leizhenyu97/WISP/Ver061/Firmware/ad7124_ble_tx_timer_LP/AD7124.h

// Low-level AD7124 register and SPI declarations for the firmware data path.
// This header defines the software shadow-register table and the helpers that read and write the device.

#ifndef _AD7124_H
#define _AD7124_H

#include "Arduino.h"

#ifdef  __cplusplus
extern "C" {
#endif

// Indexes into the software shadow-register table, not raw wire addresses.
enum ad7124_registers {
        AD7124_Status = 0x00,
        AD7124_ADC_Control,
        AD7124_Data,
        AD7124_IOCon1,
        AD7124_IOCon2,
        AD7124_ID,
        AD7124_Error,
        AD7124_Error_En,
        AD7124_Mclk_Count,
        AD7124_Channel_0,
        AD7124_Channel_1,
        AD7124_Channel_2,
        AD7124_Channel_3,
        AD7124_Channel_4,
        AD7124_Channel_5,
        AD7124_Channel_6,
        AD7124_Channel_7,
        AD7124_Channel_8,
        AD7124_Channel_9,
        AD7124_Channel_10,
        AD7124_Channel_11,
        AD7124_Channel_12,
        AD7124_Channel_13,
        AD7124_Channel_14,
        AD7124_Channel_15,
        AD7124_Config_0,
        AD7124_Config_1,
        AD7124_Config_2,
        AD7124_Config_3,
        AD7124_Config_4,
        AD7124_Config_5,
        AD7124_Config_6,
        AD7124_Config_7,
        AD7124_Filter_0,
        AD7124_Filter_1,
        AD7124_Filter_2,
        AD7124_Filter_3,
        AD7124_Filter_4,
        AD7124_Filter_5,
        AD7124_Filter_6,
        AD7124_Filter_7,
        AD7124_Offset_0,
        AD7124_Offset_1,
        AD7124_Offset_2,
        AD7124_Offset_3,
        AD7124_Offset_4,
        AD7124_Offset_5,
        AD7124_Offset_6,
        AD7124_Offset_7,
        AD7124_Gain_0,
        AD7124_Gain_1,
        AD7124_Gain_2,
        AD7124_Gain_3,
        AD7124_Gain_4,
        AD7124_Gain_5,
        AD7124_Gain_6,
        AD7124_Gain_7,
        AD7124_REG_NO
    };

     typedef enum _ad7124_reg_access{
        AD7124_RW = 1,   /* Read and Write */
        AD7124_R  = 2,   /* Read only */
        AD7124_W  = 3,   /* Write only */
    } ad7124_reg_access; // Software access permissions for entries in regs[].

    /*! Device register info */
    typedef struct _ad7124_st_reg {
        int32_t addr;   // Raw AD7124 register address used in the communication byte.
        int32_t value;  // Shadowed register value stored in software.
        uint8_t _size;  // Register payload width in bytes.
        uint8_t rw;     // Access permission from ad7124_reg_access.
    } ad7124_st_reg;

    /* AD7124 raw register addresses placed in the first SPI command byte. */
    enum AD7124_reg_map  {
        COMM_REG     = 0x00,
        STATUS_REG   = 0x00,
        ADC_CTRL_REG = 0x01,
        DATA_REG     = 0x02,
        IO_CTRL1_REG = 0x03,
        IO_CTRL2_REG = 0x04,
        ID_REG       = 0x05,
        ERR_REG      = 0x06,
        ERREN_REG    = 0x07,
        CH0_MAP_REG  = 0x09,
        CH1_MAP_REG  = 0x0A,
        CH2_MAP_REG  = 0x0B,
        CH3_MAP_REG  = 0x0C,
        CH4_MAP_REG  = 0x0D,
        CH5_MAP_REG  = 0x0E,
        CH6_MAP_REG  = 0x0F,
        CH7_MAP_REG  = 0x10,
        CH8_MAP_REG  = 0x11,
        CH9_MAP_REG  = 0x12,
        CH10_MAP_REG = 0x13,
        CH11_MAP_REG = 0x14,
        CH12_MAP_REG = 0x15,
        CH13_MAP_REG = 0x16,
        CH14_MAP_REG = 0x17,
        CH15_MAP_REG = 0x18,
        CFG0_REG     = 0x19,
        CFG1_REG     = 0x1A,
        CFG2_REG     = 0x1B,
        CFG3_REG     = 0x1C,
        CFG4_REG     = 0x1D,
        CFG5_REG     = 0x1E,
        CFG6_REG     = 0x1F,
        CFG7_REG     = 0x20,
        FILT0_REG    = 0x21,
        FILT1_REG    = 0x22,
        FILT2_REG    = 0x23,
        FILT3_REG    = 0x24,
        FILT4_REG    = 0x25,
        FILT5_REG    = 0x26,
        FILT6_REG    = 0x27,
        FILT7_REG    = 0x28,
        OFFS0_REG    = 0x29,
        OFFS1_REG    = 0x2A,
        OFFS2_REG    = 0x2B,
        OFFS3_REG    = 0x2C,
        OFFS4_REG    = 0x2D,
        OFFS5_REG    = 0x2E,
        OFFS6_REG    = 0x2F,
        OFFS7_REG    = 0x30,
        GAIN0_REG    = 0x31,
        GAIN1_REG    = 0x32,
        GAIN2_REG    = 0x33,
        GAIN3_REG    = 0x34,
        GAIN4_REG    = 0x35,
        GAIN5_REG    = 0x36,
        GAIN6_REG    = 0x37,
        GAIN7_REG    = 0x38,
    };

    /* Communication Register bits: these macros assemble the first SPI command byte. */
#define AD7124_COMM_REG_WEN    (0 << 7)
#define AD7124_COMM_REG_WR     (0 << 6)
#define AD7124_COMM_REG_RD     (1 << 6)
#define AD7124_COMM_REG_RA(x)  ((x) & 0x3F)

    /* Status Register bits */
#define AD7124_STATUS_REG_RDY          (1 << 7)
#define AD7124_STATUS_REG_ERROR_FLAG   (1 << 6)
#define AD7124_STATUS_REG_POR_FLAG     (1 << 4)
#define AD7124_STATUS_REG_CH_ACTIVE(x) ((x) & 0xF)

    /* ADC_Control Register bits */
#define AD7124_ADC_CTRL_REG_DOUT_RDY_DEL   (1 << 12)
#define AD7124_ADC_CTRL_REG_CONT_READ      (1 << 11)
#define AD7124_ADC_CTRL_REG_DATA_STATUS    (1 << 10)
#define AD7124_ADC_CTRL_REG_CS_EN          (1 << 9)
#define AD7124_ADC_CTRL_REG_REF_EN         (1 << 8)
#define AD7124_ADC_CTRL_REG_POWER_MODE(x)  (((x) & 0x3) << 6)
#define AD7124_ADC_CTRL_REG_MODE(x)        (((x) & 0xF) << 2)
#define AD7124_ADC_CTRL_REG_CLK_SEL(x)    (((x) & 0x3) << 0)

    /* IO_Control_1 Register bits */
#define AD7124_IO_CTRL1_REG_GPIO_DAT2     (1 << 23)
#define AD7124_IO_CTRL1_REG_GPIO_DAT1     (1 << 22)
#define AD7124_IO_CTRL1_REG_GPIO_CTRL2    (1 << 19)
#define AD7124_IO_CTRL1_REG_GPIO_CTRL1    (1 << 18)
#define AD7124_IO_CTRL1_REG_PDSW          (1 << 15)
#define AD7124_IO_CTRL1_REG_IOUT1(x)      (((x) & 0x7) << 11)
#define AD7124_IO_CTRL1_REG_IOUT0(x)      (((x) & 0x7) << 8)
#define AD7124_IO_CTRL1_REG_IOUT_CH1(x)   (((x) & 0xF) << 4)
#define AD7124_IO_CTRL1_REG_IOUT_CH0(x)   (((x) & 0xF) << 0)

    /*IO_Control_1 AD7124-8 specific bits */
#define AD7124_8_IO_CTRL1_REG_GPIO_DAT4     (1 << 23)
#define AD7124_8_IO_CTRL1_REG_GPIO_DAT3     (1 << 22)
#define AD7124_8_IO_CTRL1_REG_GPIO_DAT2     (1 << 21)
#define AD7124_8_IO_CTRL1_REG_GPIO_DAT1     (1 << 20)
#define AD7124_8_IO_CTRL1_REG_GPIO_CTRL4    (1 << 19)
#define AD7124_8_IO_CTRL1_REG_GPIO_CTRL3    (1 << 18)
#define AD7124_8_IO_CTRL1_REG_GPIO_CTRL2    (1 << 17)
#define AD7124_8_IO_CTRL1_REG_GPIO_CTRL1    (1 << 16)

    /* IO_Control_2 Register bits */
#define AD7124_IO_CTRL2_REG_GPIO_VBIAS7   (1 << 15)
#define AD7124_IO_CTRL2_REG_GPIO_VBIAS6   (1 << 14)
#define AD7124_IO_CTRL2_REG_GPIO_VBIAS5   (1 << 11)
#define AD7124_IO_CTRL2_REG_GPIO_VBIAS4   (1 << 10)
#define AD7124_IO_CTRL2_REG_GPIO_VBIAS3   (1 << 5)
#define AD7124_IO_CTRL2_REG_GPIO_VBIAS2   (1 << 4)
#define AD7124_IO_CTRL2_REG_GPIO_VBIAS1   (1 << 1)
#define AD7124_IO_CTRL2_REG_GPIO_VBIAS0   (1)

    /*IO_Control_2 AD7124-8 specific bits */
#define AD7124_8_IO_CTRL2_REG_GPIO_VBIAS15  (1 << 15)
#define AD7124_8_IO_CTRL2_REG_GPIO_VBIAS14  (1 << 14)
#define AD7124_8_IO_CTRL2_REG_GPIO_VBIAS13  (1 << 13)
#define AD7124_8_IO_CTRL2_REG_GPIO_VBIAS12  (1 << 12)
#define AD7124_8_IO_CTRL2_REG_GPIO_VBIAS11  (1 << 11)
#define AD7124_8_IO_CTRL2_REG_GPIO_VBIAS10  (1 << 10)
#define AD7124_8_IO_CTRL2_REG_GPIO_VBIAS9   (1 << 9)
#define AD7124_8_IO_CTRL2_REG_GPIO_VBIAS8   (1 << 8)
#define AD7124_8_IO_CTRL2_REG_GPIO_VBIAS7   (1 << 7)
#define AD7124_8_IO_CTRL2_REG_GPIO_VBIAS6   (1 << 6)
#define AD7124_8_IO_CTRL2_REG_GPIO_VBIAS5   (1 << 5)
#define AD7124_8_IO_CTRL2_REG_GPIO_VBIAS4   (1 << 4)
#define AD7124_8_IO_CTRL2_REG_GPIO_VBIAS3   (1 << 3)
#define AD7124_8_IO_CTRL2_REG_GPIO_VBIAS2   (1 << 2)
#define AD7124_8_IO_CTRL2_REG_GPIO_VBIAS1   (1 << 1)
#define AD7124_8_IO_CTRL2_REG_GPIO_VBIAS0   (1 << 0)

    /* ID Register bits */
#define AD7124_ID_REG_DEVICE_ID(x)   (((x) & 0xF) << 4)
#define AD7124_ID_REG_SILICON_REV(x) (((x) & 0xF) << 0)

    /* Error Register bits */
#define AD7124_ERR_REG_LDO_CAP_ERR        (1 << 19)
#define AD7124_ERR_REG_ADC_CAL_ERR        (1 << 18)
#define AD7124_ERR_REG_ADC_CONV_ERR       (1 << 17)
#define AD7124_ERR_REG_ADC_SAT_ERR        (1 << 16)
#define AD7124_ERR_REG_AINP_OV_ERR        (1 << 15)
#define AD7124_ERR_REG_AINP_UV_ERR        (1 << 14)
#define AD7124_ERR_REG_AINM_OV_ERR        (1 << 13)
#define AD7124_ERR_REG_AINM_UV_ERR        (1 << 12)
#define AD7124_ERR_REG_REF_DET_ERR        (1 << 11)
#define AD7124_ERR_REG_DLDO_PSM_ERR       (1 << 9)
#define AD7124_ERR_REG_ALDO_PSM_ERR       (1 << 7)
#define AD7124_ERR_REG_SPI_IGNORE_ERR     (1 << 6)
#define AD7124_ERR_REG_SPI_SLCK_CNT_ERR   (1 << 5)
#define AD7124_ERR_REG_SPI_READ_ERR       (1 << 4)
#define AD7124_ERR_REG_SPI_WRITE_ERR      (1 << 3)
#define AD7124_ERR_REG_SPI_CRC_ERR        (1 << 2)
#define AD7124_ERR_REG_MM_CRC_ERR         (1 << 1)

    /* Error_En Register bits */
#define AD7124_ERREN_REG_MCLK_CNT_EN           (1 << 22)
#define AD7124_ERREN_REG_LDO_CAP_CHK_TEST_EN   (1 << 21)
#define AD7124_ERREN_REG_LDO_CAP_CHK(x)        (((x) & 0x3) << 19)
#define AD7124_ERREN_REG_ADC_CAL_ERR_EN        (1 << 18)
#define AD7124_ERREN_REG_ADC_CONV_ERR_EN       (1 << 17)
#define AD7124_ERREN_REG_ADC_SAT_ERR_EN        (1 << 16)
#define AD7124_ERREN_REG_AINP_OV_ERR_EN        (1 << 15)
#define AD7124_ERREN_REG_AINP_UV_ERR_EN        (1 << 14)
#define AD7124_ERREN_REG_AINM_OV_ERR_EN        (1 << 13)
#define AD7124_ERREN_REG_AINM_UV_ERR_EN        (1 << 12)
#define AD7124_ERREN_REG_REF_DET_ERR_EN        (1 << 11)
#define AD7124_ERREN_REG_DLDO_PSM_TRIP_TEST_EN (1 << 10)
#define AD7124_ERREN_REG_DLDO_PSM_ERR_ERR      (1 << 9)
#define AD7124_ERREN_REG_ALDO_PSM_TRIP_TEST_EN (1 << 8)
#define AD7124_ERREN_REG_ALDO_PSM_ERR_EN       (1 << 7)
#define AD7124_ERREN_REG_SPI_IGNORE_ERR_EN     (1 << 6)
#define AD7124_ERREN_REG_SPI_SCLK_CNT_ERR_EN   (1 << 5)
#define AD7124_ERREN_REG_SPI_READ_ERR_EN       (1 << 4)
#define AD7124_ERREN_REG_SPI_WRITE_ERR_EN      (1 << 3)
#define AD7124_ERREN_REG_SPI_CRC_ERR_EN        (1 << 2)
#define AD7124_ERREN_REG_MM_CRC_ERR_EN         (1 << 1)

    /* Channel Registers 0-15 bits: map one logical channel to a setup and AINP/AINM pair. */
#define AD7124_CH_MAP_REG_CH_ENABLE    (1 << 15)
#define AD7124_CH_MAP_REG_SETUP(x)     (((x) & 0x7) << 12)
#define AD7124_CH_MAP_REG_AINP(x)      (((x) & 0x1F) << 5)
#define AD7124_CH_MAP_REG_AINM(x)      (((x) & 0x1F) << 0)

    /* Configuration Registers 0-7 bits: polarity, buffering, reference source, and PGA. */
#define AD7124_CFG_REG_BIPOLAR     (1 << 11)
#define AD7124_CFG_REG_BURNOUT(x)  (((x) & 0x3) << 9)
#define AD7124_CFG_REG_REF_BUFP    (1 << 8)
#define AD7124_CFG_REG_REF_BUFM    (1 << 7)
#define AD7124_CFG_REG_AIN_BUFP    (1 << 6)
#define AD7124_CFG_REG_AINN_BUFM   (1 << 5)
#define AD7124_CFG_REG_REF_SEL(x)  ((x) & 0x3) << 3
#define AD7124_CFG_REG_PGA(x)      (((x) & 0x7) << 0)

    /* Filter Registers 0-7 bits: filter type, post-filter, single-cycle mode, and full-scale rate. */
#define AD7124_FILT_REG_FILTER(x)        ((uint32_t)((x) & 0x7) << 21)
#define AD7124_FILT_REG_REJ60             ((uint32_t)1 << 20)
#define AD7124_FILT_REG_POST_FILTER(x)    ((uint32_t)((x) & 0x7) << 17)
#define AD7124_FILT_REG_SINGLE_CYCLE      ((uint32_t)1 << 16)
#define AD7124_FILT_REG_FS(x)             ((uint32_t)((x) & 0x7FF) << 0)

#define AD7124_CRC8_POLYNOMIAL_REPRESENTATION 0x07 /* CRC polynomial x8 + x2 + x + 1. */
#define AD7124_DISABLE_CRC 0                    /* Driver mode: do not append or verify CRC. */
#define AD7124_USE_CRC 1                        /* Driver mode: append and verify CRC bytes. */
#define AD7124_READ_DATA 2                      /* Driver mode token for data-read transfers. */

#define INVALID_VAL -1 /* Invalid argument */
#define COMM_ERR    -2 /* Communication error on receive */
#define TIMEOUT     -3 /* A timeout has occured */

/**
 * Initializes the driver globals and default runtime settings.
 *
 * @return None.
 */
void AD7124_Init();

/**
 * Issues the AD7124 serial-interface reset sequence.
 *
 * @return 0 on success or a negative error code.
 */
int32_t AD7124_Reset();

/**
 * Reads and returns the value of a shadowed device register.
 *
 * @param reg Register index to read.
 * @return Shadowed register value.
 */
uint32_t AD7124_ReadDeviceRegister(enum ad7124_registers reg);

/**
 * Updates a shadowed device register and writes it to hardware.
 *
 * @param reg Register index to write.
 * @param value Register value to store and transmit.
 * @return 0 on success or a negative error code.
 */
int32_t AD7124_WriteDeviceRegister(enum ad7124_registers reg, uint32_t value);

/**
 * Reads one register, polling for SPI readiness when enabled.
 *
 * @param pReg Pointer to the register descriptor to update.
 * @return 0 on success or a negative error code.
 */
int32_t AD7124_ReadRegister(ad7124_st_reg* pReg);

/**
 * Writes one register, polling for SPI readiness when enabled.
 *
 * @param pReg Register descriptor containing the value to write.
 * @return 0 on success or a negative error code.
 */
int32_t AD7124_WriteRegister(ad7124_st_reg pReg);

/**
 * Reads one register without SPI-ready polling.
 *
 * @param pReg Pointer to the register descriptor to update.
 * @return 0 on success or a negative error code.
 */
int32_t AD7124_NoCheckReadRegister(ad7124_st_reg* pReg);

/**
 * Writes one register without SPI-ready polling.
 *
 * @param reg Register descriptor containing the value to write.
 * @return 0 on success or a negative error code.
 */
int32_t AD7124_NoCheckWriteRegister(ad7124_st_reg reg);

/**
 * Polls until the AD7124 can accept another SPI transaction.
 *
 * @param timeout Maximum poll count before returning.
 * @return 0 on success or a positive/negative timeout or error code.
 */
int32_t AD7124_WaitForSpiReady(uint32_t timeout);

/**
 * Polls until a new conversion result is available.
 *
 * @param timeout Maximum poll count before returning.
 * @return 0 on success or a negative timeout/error code.
 */
int32_t AD7124_WaitForConvReady(uint32_t timeout);

/**
 * Reads the current conversion result register.
 *
 * @param pData Output pointer for the conversion result.
 * @return 0 on success or a negative error code.
 */
int32_t AD7124_ReadData(int32_t* pData);

/**
 * Computes the CRC checksum for a buffer.
 *
 * @param pBuf Data buffer.
 * @param bufSize Buffer length in bytes.
 * @return Computed CRC byte.
 */
uint8_t AD7124_ComputeCRC8(uint8_t* pBuf, uint8_t bufSize);

/**
 * Derives the SPI-ready polling mode from the enabled error bits.
 *
 * @return None.
 */
void AD7124_UpdateDevSpiSettings();

/**
 * Resets the AD7124 and writes the configured startup register set.
 *
 * @return 0 on success or a negative error code.
 */
int32_t AD7124_Setup();

/**
 * Dispatches a read transfer to the currently selected SPI target.
 *
 * @param data Transfer buffer.
 * @param bytes_number Number of bytes to transfer.
 * @return Number of bytes transferred.
 */
uint8_t AD7124_SPI_Read(uint8_t *data, uint8_t bytes_number);

/**
 * Dispatches a write transfer to the currently selected SPI target.
 *
 * @param data Transfer buffer.
 * @param bytes_number Number of bytes to transfer.
 * @return Number of bytes transferred.
 */
uint8_t AD7124_SPI_Write(uint8_t *data, uint8_t bytes_number);

/**
 * Reserved stub for future AD7124 sync/filter-reset support.
 *
 * @return None.
 */
void ad7124_sync();

extern ad7124_st_reg *regs; // Pointer to the active AD7124 shadow-register table.

#ifdef  __cplusplus
}
#endif // __cplusplus

#endif
